ValentiWorkLearning/GradWork/Images/Design/v1.1_Render/HealthPage.jpg

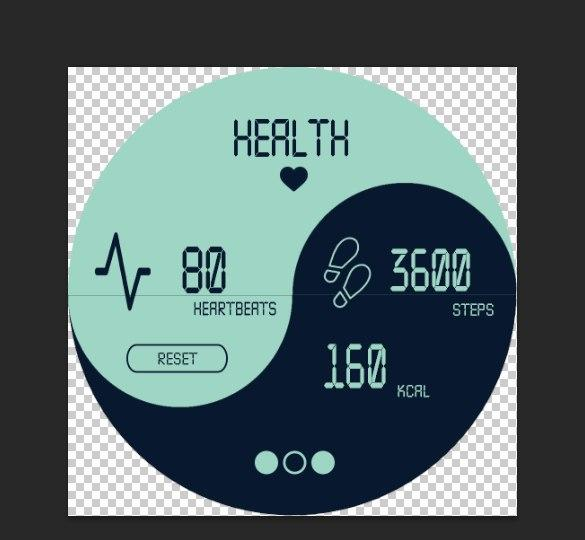
Images/Design/v1.1_Render/HealthPage.jpg
