ValentiWorkLearning/GradWork/Images/photo_2019-11-03_00-30-05.jpg

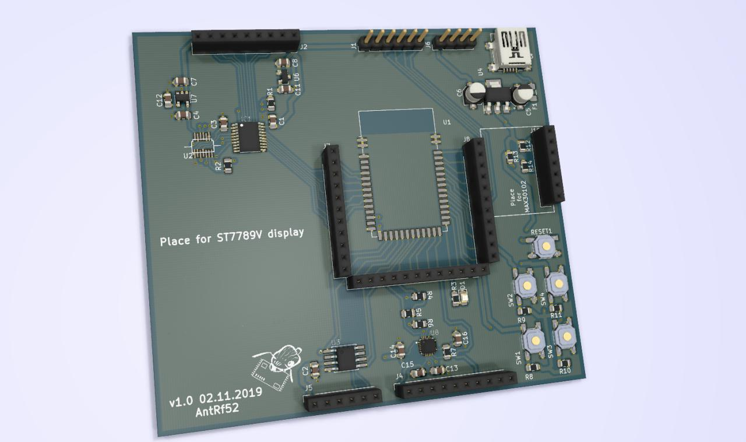
Images/photo_2019-11-03_00-30-05.jpg
