ValentiWorkLearning/GradWork/Images/photo_2019-11-03_00-31-58.jpg

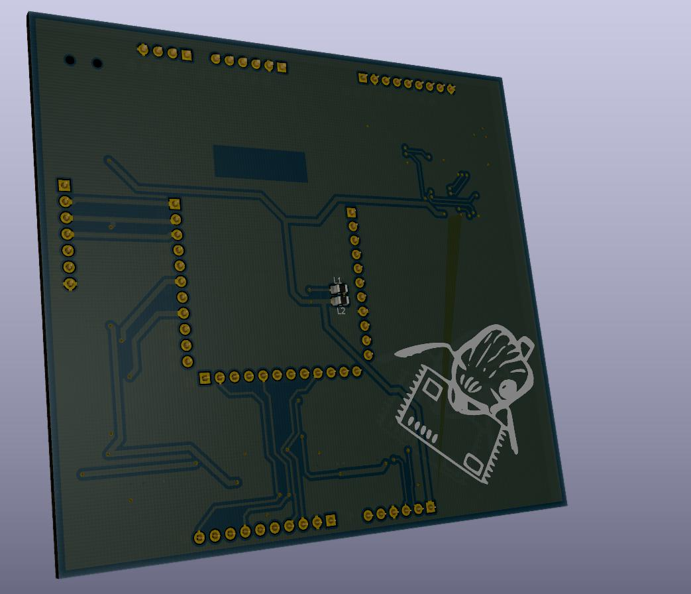
Images/photo_2019-11-03_00-31-58.jpg
