ValentiWorkLearning/GradWork/Images/photo_2020-01-09_01-23-37.jpg

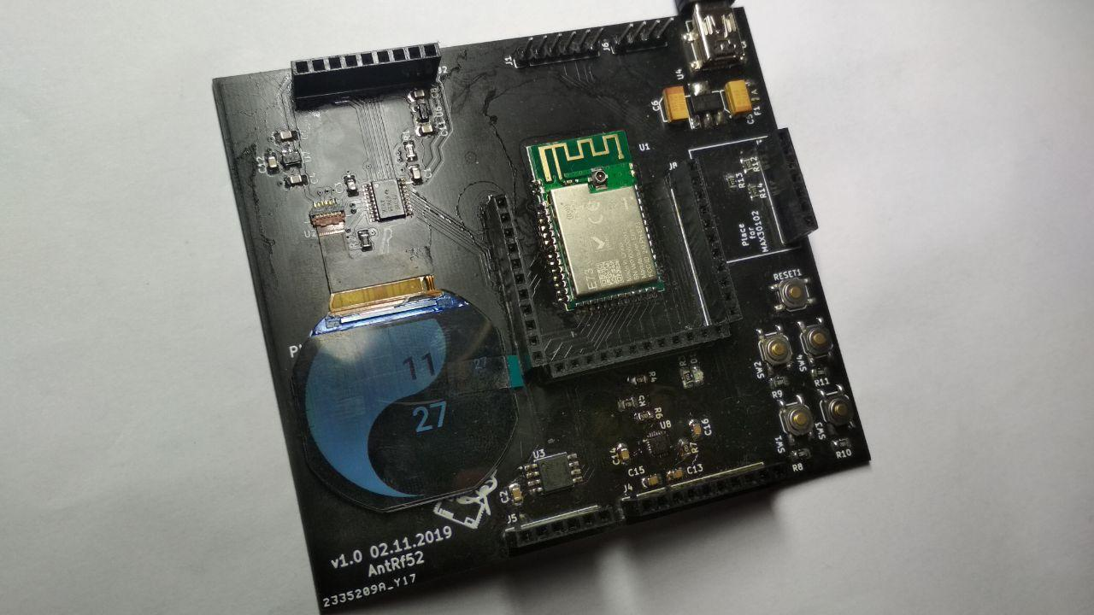
Images/photo_2020-01-09_01-23-37.jpg
