ValentiWorkLearning/GradWork/Images/Снимок1.JPG

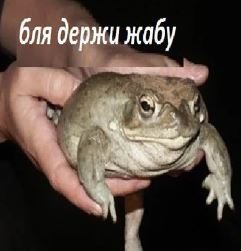
Images/Снимок1.JPG
