ValentiWorkLearning/GradWork/Images/Снимок.JPG

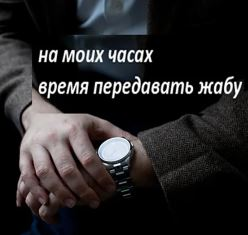
Images/Снимок.JPG
