ValentiWorkLearning/GradWork/Firmware/firmware_tests/drivers/windond_flash/flash_driver_test_suite.cpp

#include <gmock/gmock.h>
#include <gtest/gtest.h>

#include <random>

#include "flash_fixture.hpp"

#include <array>
#include <utils/CoroUtils.hpp>
#include <utils/coroutine/SyncWait.hpp>

using ::testing::ContainerEq;
using ::testing::Return;

TEST_F(FlashDriverTest, RequestJedecId)
{
    EXPECT_CALL(getMockGpio(), setGpioLow()).Times(1);
    EXPECT_CALL(getMockGpio(), setGpioHigh()).Times(1);

    TDataStream ExpectedStream{std::byte(0xEF), std::byte(0x40), std::byte(0x18)};

    EXPECT_CALL(spiMockAccess(), receivedData)
        .Times(1)
        .WillOnce(Return(std::span(
            reinterpret_cast<const std::uint8_t*>(ExpectedStream.data()), ExpectedStream.size())));

    auto fToJedecId = [](const TDataStream& _jedecId) {
        std::uint32_t result{};
        result |= std::to_integer<std::uint32_t>(_jedecId[0]) << 16;
        result |= std::to_integer<std::uint32_t>(_jedecId[1]) << 8;
        result |= std::to_integer<std::uint32_t>(_jedecId[2]);

        return result;
    };

    auto jedecId = CoroUtils::syncWait(flashDriver.requestJEDEDCId());
    EXPECT_EQ(jedecId, fToJedecId(ExpectedStream));
}

MATCHER_P(SpanChecker, spanItem, "Span content equals")
{
    const auto argEl{std::get<0>(arg)};
    const bool isEqual = std::equal(spanItem.begin(), spanItem.end(), argEl.begin());
    return isEqual;
}
TEST_F(FlashDriverTest, RequestWriteBlock)
{

    EXPECT_CALL(getMockGpio(), setGpioLow()).Times(1);
    EXPECT_CALL(getMockGpio(), setGpioHigh()).Times(1);

    auto TransmitData{std::array<std::uint8_t, 7>{0xEF, 0xFF, 0x18, 0x19, 0x20, 0x21, 0x22}};

    constexpr std::uint32_t address{0x10'00};

    constexpr std::size_t WriteEnableCommandLength = 1;
    constexpr const std::array<std::uint8_t, WriteEnableCommandLength> writeEnableCommand{
        WindbondCommandSet::WriteEnable};

    constexpr std::size_t ProgramPageCommandLength = 4;
    constexpr const std::array<std::uint8_t, ProgramPageCommandLength> pageProgramCommand{
        WindbondCommandSet::PageProgram,
        static_cast<std::uint8_t>(address & 0x00'FF'00'00 >> 16),
        static_cast<std::uint8_t>(address & 0x00'00'FF'00 >> 8),
        static_cast<std::uint8_t>(address & 0x00'00'00'FF)};

    testing::Sequence sequence;

    // https://gist.github.com/cppengineer/f1b6bc0f04ac7c29e963364f2c564a5e

    const auto writeEnableSpan =
        std::span<const std::uint8_t>(writeEnableCommand.data(), writeEnableCommand.size());

    const auto ProgramCommandSpan =
        std::span<const std::uint8_t>(pageProgramCommand.data(), pageProgramCommand.size());
    EXPECT_CALL(spiMockAccess(), sentData)
        .With(SpanChecker(writeEnableSpan))
        .Times(1)
        .InSequence(sequence);

    EXPECT_CALL(spiMockAccess(), sentData)
        .With(SpanChecker(ProgramCommandSpan))
        .Times(1)
        .InSequence(sequence);
    EXPECT_CALL(spiMockAccess(), sentData)
        .With(SpanChecker(std::span(TransmitData.data(), TransmitData.size())))
        .Times(1)
        .InSequence(sequence);

    auto task = flashDriver.pageWrite(address, std::span(TransmitData.data(), TransmitData.size()));
    CoroUtils::syncWait(task);
}

TEST_F(FlashDriverTest, RequestReadBlock)
{

    EXPECT_CALL(getMockGpio(), setGpioLow()).Times(1);
    EXPECT_CALL(getMockGpio(), setGpioHigh()).Times(1);

    using TStream = std::array<std::uint8_t, 7>;

    auto ReceiveData{TStream{0xEF, 0xFF, 0x18, 0x19, 0x20, 0x21, 0x22}};

    auto Dummy{TStream{}};

    EXPECT_CALL(spiMockAccess(), receivedData)
        .Times(1)
        .WillOnce(Return(std::span(
            reinterpret_cast<const std::uint8_t*>(ReceiveData.data()), ReceiveData.size())));

    constexpr std::uint32_t address{0x10'00};

    constexpr std::size_t ReadCommandLength = 4;
    constexpr const std::array<std::uint8_t, ReadCommandLength> readCommand{
        WindbondCommandSet::ReadData,
        static_cast<std::uint8_t>((address & 0x00'FF'00'00) >> 16),
        static_cast<std::uint8_t>((address & 0x00'00'FF'00) >> 8),
        static_cast<std::uint8_t>(address & 0x00'00'00'FF)};

    testing::Sequence sequence;

    // https://gist.github.com/cppengineer/f1b6bc0f04ac7c29e963364f2c564a5e

    const auto DummySpan = std::span<const std::uint8_t>(Dummy.data(), Dummy.size());

    const auto ReadDataSpan = std::span<const std::uint8_t>(readCommand.data(), readCommand.size());

    EXPECT_CALL(spiMockAccess(), sentData)
        .With(SpanChecker(ReadDataSpan))
        .Times(1)
        .InSequence(sequence);
    EXPECT_CALL(spiMockAccess(), sentData)
        .With(SpanChecker(std::span(DummySpan.data(), DummySpan.size())))
        .Times(1)
        .InSequence(sequence);

    auto task = flashDriver.requestReadBlock(address, ReceiveData.size());
    auto readSpan = CoroUtils::syncWait(task);

    EXPECT_TRUE(
        std::equal(readSpan.begin(), readSpan.end(), ReceiveData.begin(), ReceiveData.end()));
}
