ValentiWorkLearning/GradWork/Firmware/firmware_tests/drivers/windond_flash/flash_fixture.hpp

#pragma once
#include <gtest/gtest.h>

#include <backends/spi_backend_desktop.hpp>
#include <spi/spi_wrapper_async_templated.hpp>

#include <windbondflash/winbond_flash_templated.hpp>

#include <string>
#include <tuple>
#include <vector>

// TODO Fix include more clearly
#include "../spi/spi_fake_backend.hpp"
#include "../spi/mock_gpio.hpp"

class FlashDriverTest : public ::testing::Test
{

public:
    using TFlashTestDriver = ExternalFlash::WinbondFlashDriver<
        Interface::SpiTemplated::SpiBus<Testing::Spi::SpiBusBackendStub>>;
    using TDataStream = std::vector<std::byte>;

protected:
    void SetUp() override
    {
    }

    decltype(auto) getMockGpio()
    {
        return flashDriver.getSpiBus()->getBackendImpl().accesToCsPin();
    }

    decltype(auto) spiMockAccess()
    {
        return flashDriver.getSpiBus()->getBackendImpl().accessToSpiMock();
    }

    TDataStream TransactionsToDataStream()
    {
        return flashDriver.getSpiBus()->getBackendImpl().getTransmittedData();
    }

protected:
    TFlashTestDriver flashDriver;
};
